SolderedElectronics/CONNECT-programmer-hardware-design/OUTPUTS/V1.1.1/333073.jpg

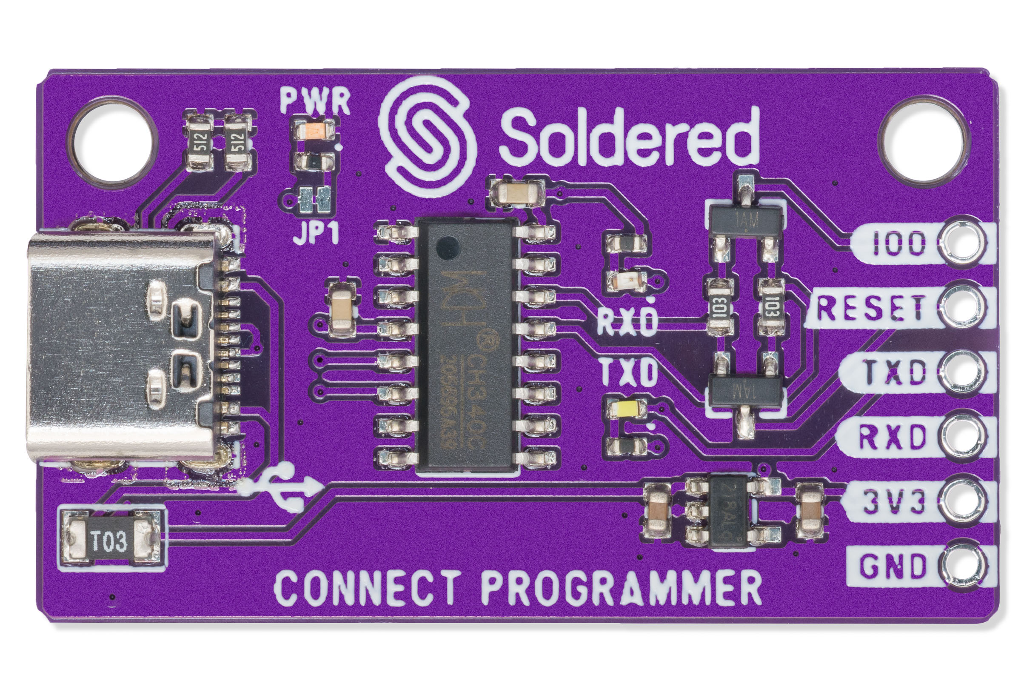
OUTPUTS/V1.1.1/333073.jpg
