SolderedElectronics/CONNECT-programmer-hardware-design/OUTPUTS/V1.1.1/CONNECT programmer Pinout.jpg

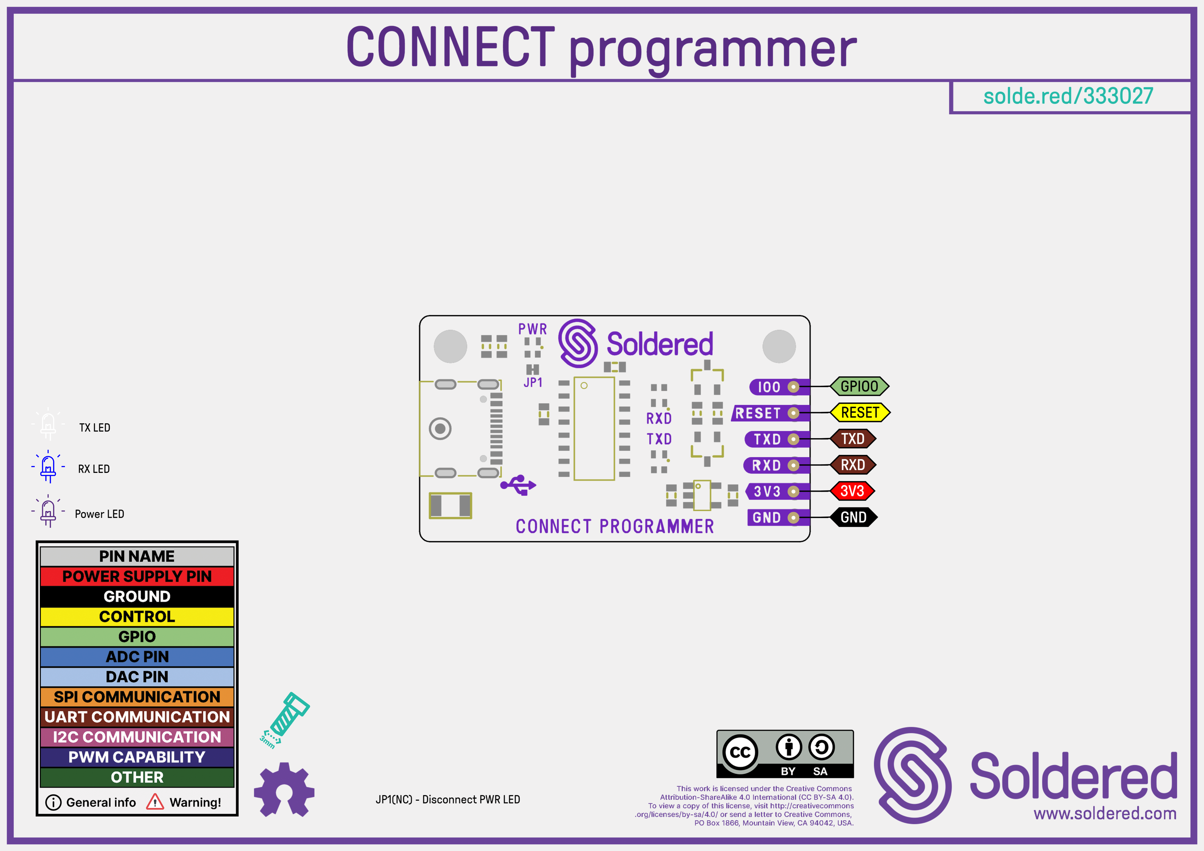
OUTPUTS/V1.1.1/CONNECT programmer Pinout.jpg
